rafae2k/Ultracif/Bibliografia/Arquivos PDF/N95 Filtering Facepiece Respirator Ultraviolet Germicidal Irradiation (UVGI) Process for Decontamination and Reuse.pdf

# N95 Filtering Facepiece Respirator Ultraviolet Germicidal Irradiation (UVGI) Process for Decontamination and Reuse

John J Lowe, Katie D Paladino, Jerald D Farke, Kathleen Boulter, Kelly Cawcutt, Mark Emodi, Shawn Gibbs, Richard Hankins, Lauren Hinkle, Terry Micheels, Shelly Schwedhelm, Angela Vasa, Michael Wadman, Suzanne Watson, and Mark E Rupp

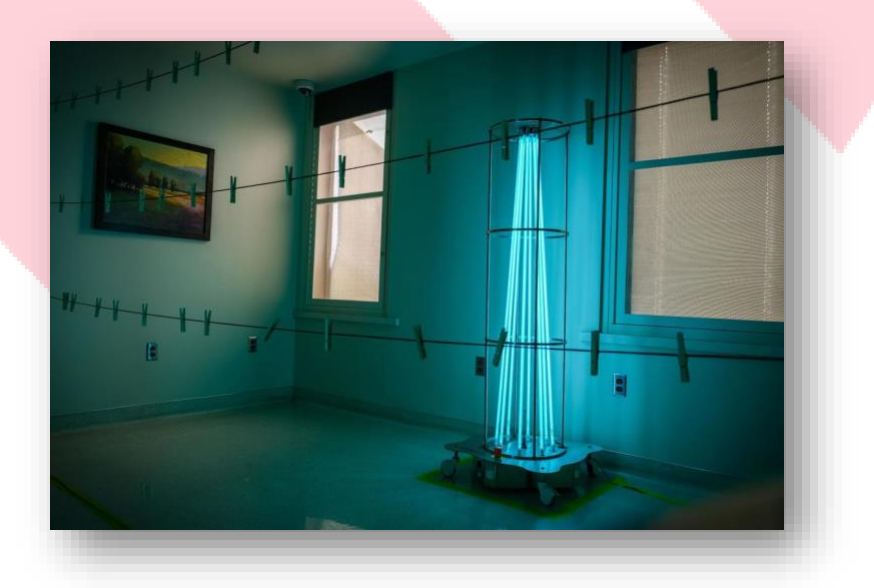
[picture p40: figure]

## Contents

## Table of Figures

Figure 1 – Room Setup (Overhead View). The lines holding the N95 FFRs are 13 feet long and hold 30 respirators per line (3 across the room); the UVGI “torches” are located 4 feet from the

Figure 6 – Log respirator drop-off (must note contact for pickup of respirators when

Figure 8 – Indicate name of respirator owner on new white bag, and number of respirators to

Figure 9 – Wipe cart thoroughly with Oxivir®
1 wipes. Doff at threshold and exit room. Perform

Figure 13 – While cycle runs, write name on new brown bag and place in corresponding labeled

Figure 14 – Run cycle until dose is not less than 300 mJ/cm²

Figure 21 – Contact staff indicated on drop-off log to communicate respirators are ready for

## Introduction

### Rationale and Method:

The ongoing pandemic of SARS-CoV-2 resulting in COVID-19 has severely stressed the worldwide healthcare system and has created dangerous shortages of personal protective equipment (PPE) including N95 filtering facepiece respirators (N95 FFRs). In an effort to extend the stockpile of N95 FFRs at our institution and reduce risks associated with reuse of untreated, contaminated N95 FFRs, we developed a surface decontamination procedure involving the delivery of ultraviolet germicidal irradiation (UVGI) to used N95 FFRs. The evidence base supporting this program includes: 1) UVGI has been shown to effectively inactivate a wide range of human pathogens including coronaviruses and other human respiratory viruses; 2) UVGI has been demonstrated to inactivate human respiratory viruses, including coronaviruses, on various models of N95 FFRs; 3) levels of UVGI needed to inactive human respiratory viruses are well below the level of irradiation that adversely affects the fit and filtration characteristics of N95 FFRs; and 4) UVGI can be safely administered when appropriate safeguards are in place. We also recognize there is uncertainty regarding how long an N95 FFR maintains properties to achieve adequate fit, requiring providers to inspect FFRs before and after reuse. Any organization considering a decontamination strategy (including UVGI, vaporized hydrogen peroxide, warm moist heat, etc.) to deal with lack of supply or potential lack of N95 FFR should validate their own procedures, including desired surrogate microbial reduction and retained filter efficiency and fit. Herein, we briefly describe our procedure to surface decontaminate and reuse N95 FFRs.

Literature supports UVGI exposures of 1 J/cm²
are capable of decontaminating influenza virus on N95 FFRs and exposures as low as of 2-5 mJ/cm²
are capable inactivating coronaviruses on surfaces (1-2). Given this range, we validated FFR UVGI exposures of 60 mJ/cm²
and 300
mJ/cm²
, from room sensors not from the surface of each mask, to reduce 6 log of bacterial and viral surrogate organisms. In our decontamination process, used N95 FFRs are subjected to UVGI at a room exposure of 300 mJ/cm²
. This exposure is measured for one of the two UVGI sources and from a location that receives the lowest UVGI dose---this does not represent the dose on the surface of each N95 FFR. Exposure mapping of our system indicated N95 FFR received a dose of double the measured dose from each side of the N95 FFR. Single-stranded RNA viruses, such as SARS-CoV-2, are generally inactivated by UVGI exposure of 2-5 mJ/cm² (2). Thus, the UVGI exposure we have chosen exceeds, by at least several fold, the amount of exposure needed to inactivate SARS-CoV-2 and provides a wide margin of safety for surface decontamination.

Respirators are secured on wires that are strung across a room with two UVGI towers (ClorDiSys UVGI Light System, https://www.clordisys.com/products.php) on either side. Each of the two UVGI towers are equipped with eight 254 nm bulbs, these bulbs are routinely used in biosafety cabinets and produce 200 μw/cm²
at 10 feet distance for a dosage of 12 mJ/minute. We monitor the delivered UVGI exposure dose with a room UVGI meter that can be initiated and monitored from outside the room to verify that the desired exposure has been achieved. As UVGI can cause damage to eyes and skin, this protects our UVGI associate’s safety. We plan to decontaminate and reuse the N95 FFRs multiple times until respirator fit is impacted (3-5). Prior to initiating the decontamination program, the walls and ceiling were covered with a UV-reflective coating (https://lumacept.com) with which our group had experience (5). Our program initially involved the units with high N95 FFR use such as the emergency department and our COVID-19 ward, but we plan to rapidly expand to ambulatory settings. We believe a variety of UV light sources could be used in a similar fashion including UV equipped biosafety or sterilization cabinets or other UV disinfection systems and that this method can be applied to a variety of other critical items such as procedure masks. The method described below is a result of multiple tests, a review of the scientific literature, and incorporation of current institutional practice.

## UVGI Room Setup

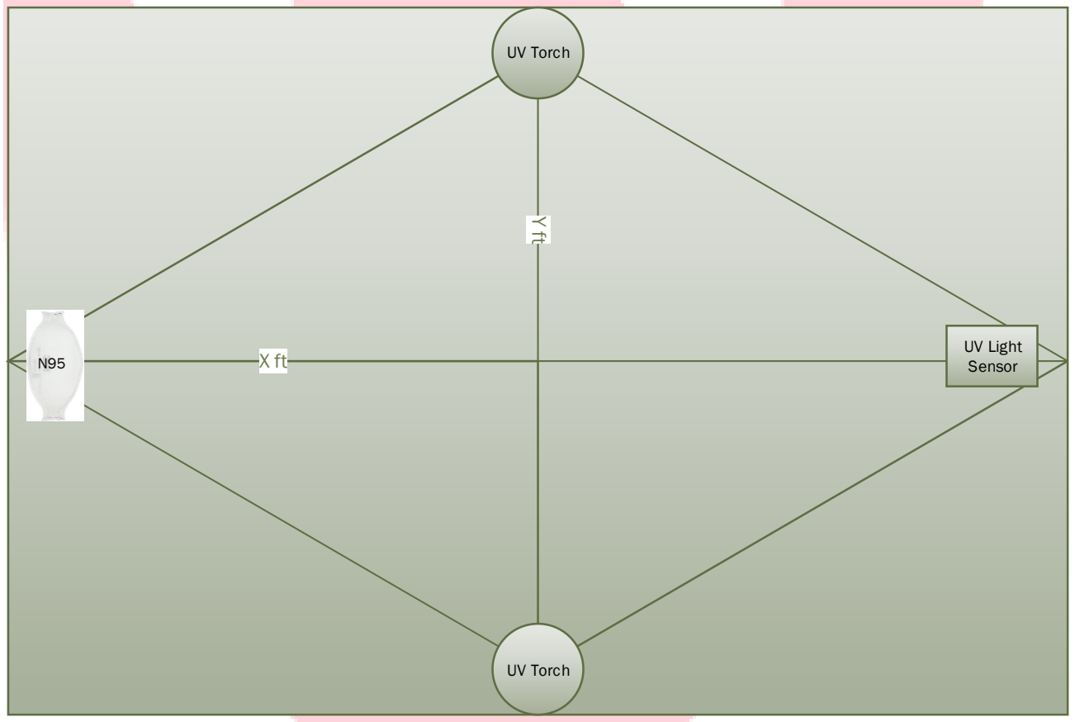
[picture p41: figure]
UV Torch; UV Torch Y ft; UV Light; Sensor

Figure 1 – Room Setup (Overhead View). The lines holding the N95 FFRs are 13 feet long and hold 30 respirators per line (3 across the room); the UVGI “torches” are located 4 feet from the center of the line and are 8 feet apart.

## Process Map

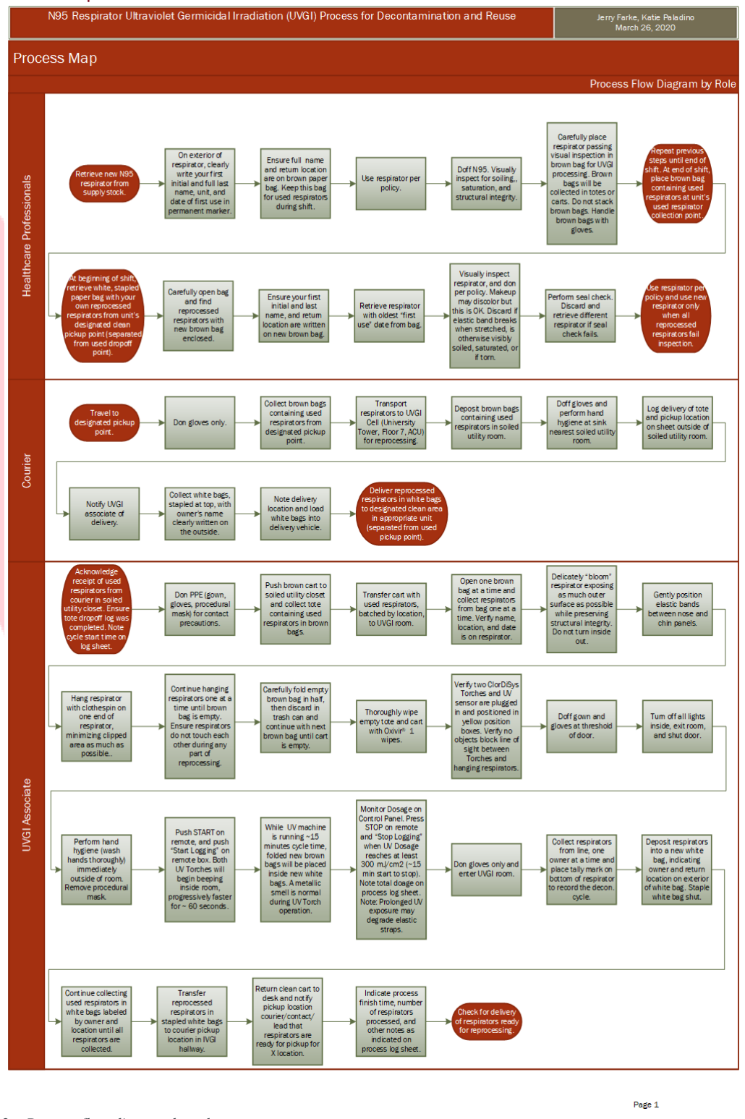
[picture p42: figure]

Figure 2 – Process flow diagram by role

## Roles

### Healthcare Professional (HCP)

- Healthcare Professional retrieves new N95 FFR from secure Omnicell storage or other storage location
- Using a permanent marker, HCP writes needed information on front of respirator including first initial and last name, department/unit location*, and date of first use*. (This ensures correct respirator is returned to correct HCP and to the correct location; Date of first use is requested to monitor duration of use as well as number of decontamination cycles)
- HCP dons N95 FFR per policy ensuring integrity of respirator and proper fit
- HCP uses N95 FFR following extended use guidelines per policy (https://www.nebraskamed.com/sites/default/files/documents/covid-19/COVID-Extended-Use-Reuse-of-PPE-and-N95.pdf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) (https://www.nebraskamed.com/sites/default/files/documents/covid-19/COVID-Extended-Use-Reuse-of-PPE-and-N95.pdf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)
Upon doffing:
- Remove N95 FFR following appropriate doffing guidelines
- Place used N95 FFR in brown paper bag ensuring brown bag is correctly labeled with HCP full name, and Department/Unit return location
- When ready to send brown bag, with used respirators, for decontamination, the HCP brings bag to department/unit designated “dirty” drop off location. This is separate from the department/unit “clean” location.
Specific to In-House Staff
- Donning gloves only, staff courier collects all used respirators (in brown bags) in a cart or tote.
- Staff courier takes cart/tote to Decontamination Unit. Only gloves need to be worn for this process.
- Staff courier places department/unit supply of brown bags (containing used respirators) in the Decontamination Unit’s Dirty Storage area. Staff courier places tote or individual bags on the shelf designated for specific unit.
- Staff courier removes gloves and performs hand hygiene
- Staff courier logs requested information onto the drop off log sheet (name of individual dropping off, contact number, department/unit location, name of person to contact for pick up, pick up contact number)
Specific to Ambulatory Clinic and Immediate Care Clinic Staff
- Lidded tote, with brown bags containing used respirators, is picked up by courier from clinic site’s designated location. Pick-ups are done at times specific to clinic site. Any used respirators, needing decontaminated, must be placed in tote prior to the specified pick up time.

Upon Completion of Decontamination Process:
Specific to In-House Staff
- The Decontamination unit calls contact person, provided on log sheet, to notify that department/unit decontaminated respirators are ready for pick up.
- Staff courier dons gloves and retrieves decontaminated respirators from the Decontamination Unit’s designated clean pick up area.

- Decontaminated respirators are in new, clean white bags displaying HCP’s and return location. A new brown bag is included in the clean white bag to serve as new “dirty” discard brown bag.
- Staff courier logs name and time of pick up on the log sheet
- White bags are returned to department/unit designated clean pick up location.
- HCP will notice a tally mark has been added, by the UVGI associate, after decontamination process, to track the number of times a particular mask has gone through the decontamination.

Specific to Ambulatory Clinic and Immediate Care Clinic Staff
- Clean white bags (containing decontaminated respirators) are returned, by courier, to each site’s designated “clean” delivery location. White bags are labeled (by decontamination personnel) with each HCP’s name and site location. A new brown bag is included in the clean white bag to serve as new “dirty” discard brown bag.
- HCP will notice a tally mark has been added, by the UVGI associate, after decontamination process, to track the number of times a particular mask has gone through the decontamination.
- Deliveries to clinic or ICC site are conducted at a time specific to site location.

* A note specific to in-house float staff: For HCP floating between multiple units, HCP may designate their unit/department as the most recently worked resulting in their white bag, with decontaminated bags, being returned to that location or, HCP may write “Float” as their unit/department location. For HCP that designate their location as “Float”, their white bag, with decontaminated respirators, need be picked up personally in the Decontamination Unit’s clean storage location designated for float staff.

### UVGI Associate

- Acknowledge receipt of used respirators from courier in soiled utility closet. Ensure tote drop-off log was completed. Note cycle start time on log sheet.
- Don PPE (gown, gloves, procedural mask) for contact precautions.
- Push brown cart to soiled utility closet and collect tote containing used respirators in brown bags.
- Transfer cart with used respirators, batched by location, to UVGI room.
- Open one brown bag at a time and collect respirators from bag one at a time. Verify name, location, and date is on respirator.
- Delicately “bloom” respirator exposing as much outer surface as possible while preserving structural integrity. Do not turn inside out.
- Gently position elastic bands between nose and chin panels, if applicable.
- Hang respirator with clothespin on one end of respirator, minimizing the clipping area as much as possible.
- Continue hanging respirators one at a time until brown bag is empty. Ensure respirators do not touch each other during any part of reprocessing.
- Carefully fold empty brown bag in half, then discard in trash can and continue with next brown bag until cart is empty.

- Thoroughly wipe empty tote and cart with Oxivir® 1 wipes.
- Verify two ClorDiSys Torches and UVGI sensor are plugged in and positioned in yellow position boxes. Verify no objects block line of sight between Torches and hanging respirators.
- Doff gown and gloves at threshold of door.
- Turn off all lights inside, exit room, and shut door.
- Perform hand hygiene (wash hands thoroughly) immediately outside of room. Remove procedural mask.
- Push START on remote, and push “Start Logging” on UVGI meter box. Both UVGI Torches will begin beeping inside room, progressively faster for ~ 60 seconds.
- While UVGI machine is running ~5 minutes cycle time, folded new brown bags will be placed inside new white bags. A metallic smell is normal during UV Torch operation.
- Monitor Dosage on Control Panel. Press STOP on remote and “Stop Logging” when UV Dosage reaches at least 300 mJ/cm² (~5-6 min start to stop). Note elapsed time and total dosage on process log sheet. Note: Prolonged UVGI exposure may degrade elastic straps.
- Don gloves only and enter UVGI room.
- Collect respirators from line, one owner at a time and place tally mark on bottom of respirator to record the decontamination cycle.
- Deposit respirators into a new white bag, indicating owner and return location on exterior of white bag. Staple white bag shut.
- Continue collecting used respirators in white bags labeled by owner and location until all respirators are collected.
- Transfer reprocessed respirators in stapled white bags to courier clean pickup location in UVGI hallway.
- Return clean cart to desk and notify pickup location courier/contact/lead that respirators are ready for pickup for their location.
- Indicate process finish time, number of respirators processed, and other notes as indicated on process log sheet.
- Check for delivery of respirators ready for reprocessing.

## Appendix

### Process Photos

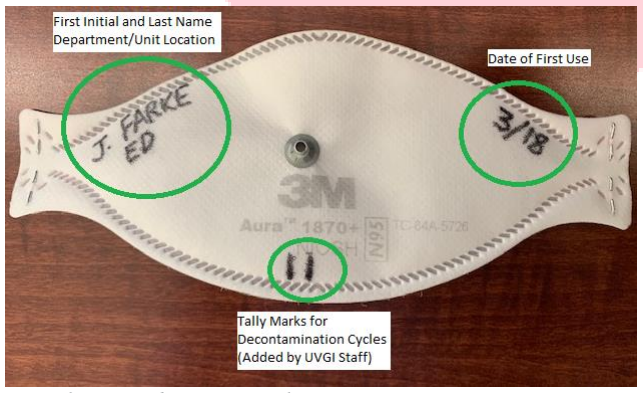
[picture p43: figure]

Figure 3 - Required respirator markings.

Courier

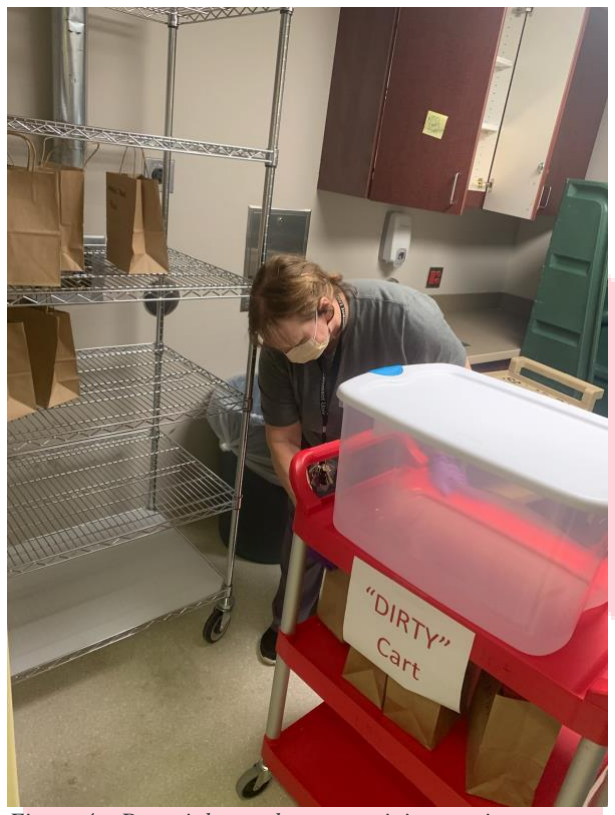
[picture p44: figure]

Figure 4 – Deposit brown bags containing respirators on rack in soiled utility room.

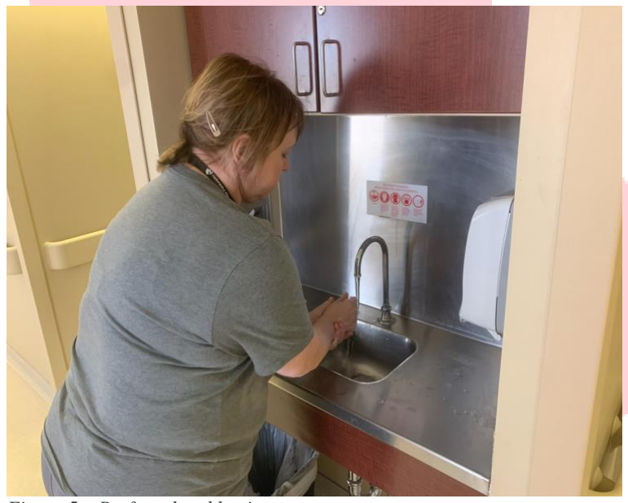
[picture p45: figure]

Figure 5 – Perform hand hygiene.

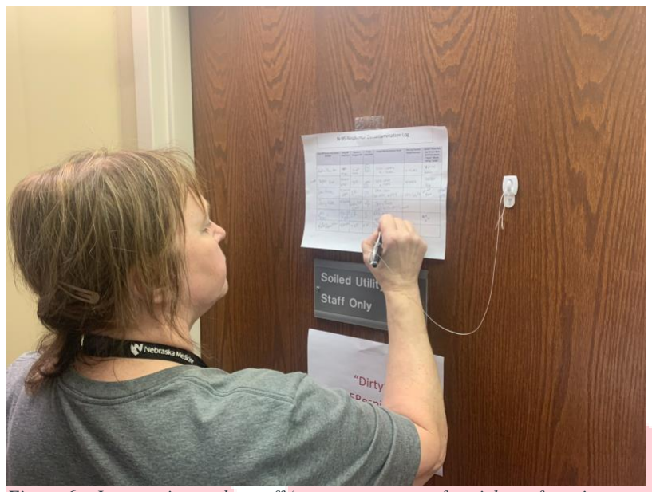
[picture p46: figure]

Figure 6 – Log respirator drop-off (must note contact for pickup of respirators when decontaminated).
UVGI Associate

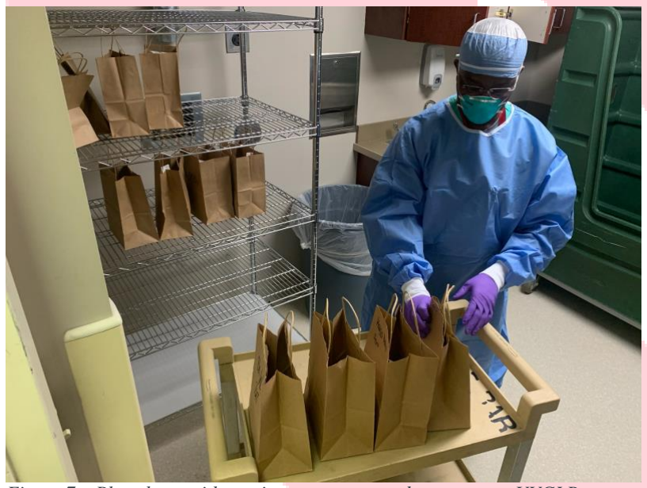
[picture p47: figure]

Figure 7 – Place bags with respirators on cart and transport to UVGI Room.

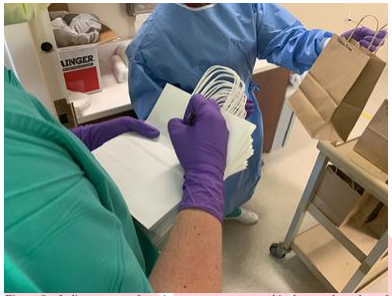
[picture p48: figure]

Figure 8 – Indicate name of respirator owner on new white bag, and number of respirators to return.

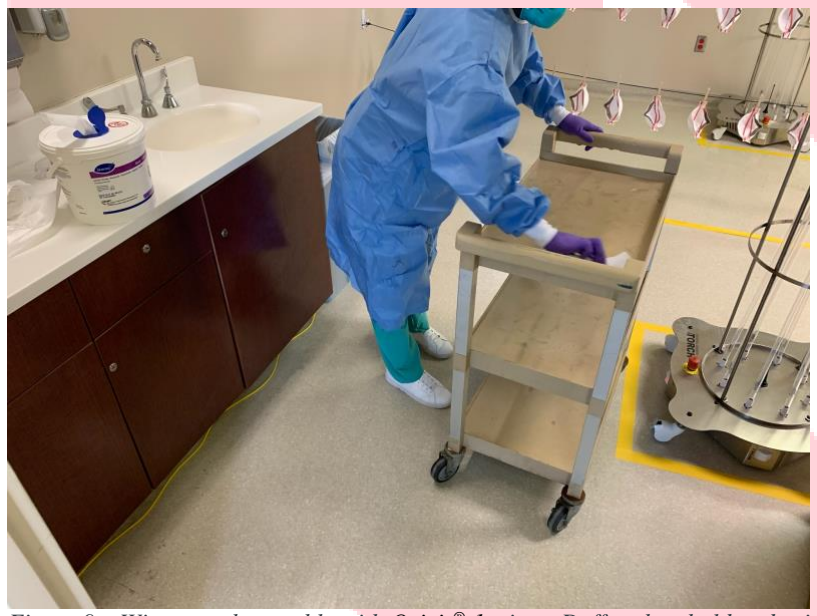
[picture p49: figure]

Figure 9 – Wipe cart thoroughly with Oxivir® 1 wipes. Doff at threshold and exit room. Perform hand hygiene.

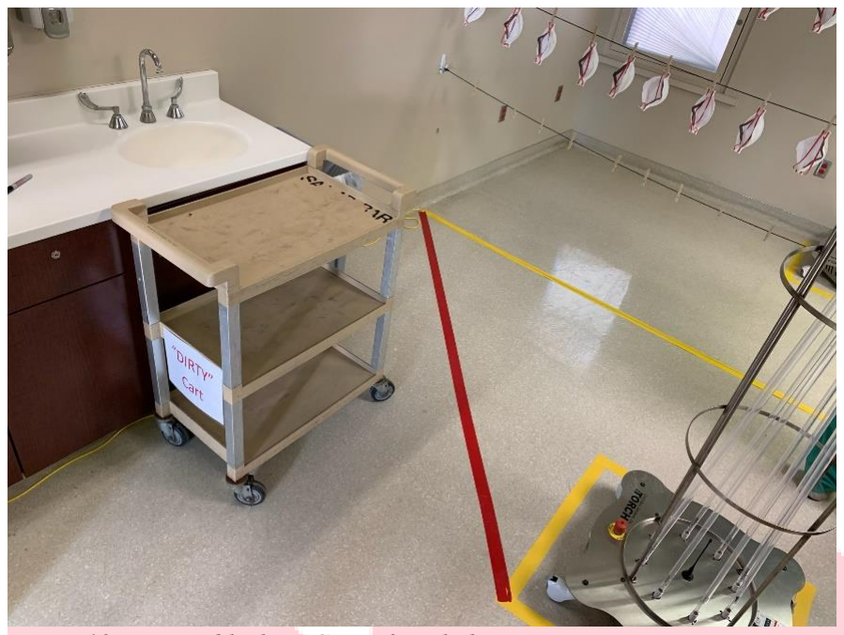
[picture p50: figure]

Figure 10 – Do not block UVGI arc from light to respirators.

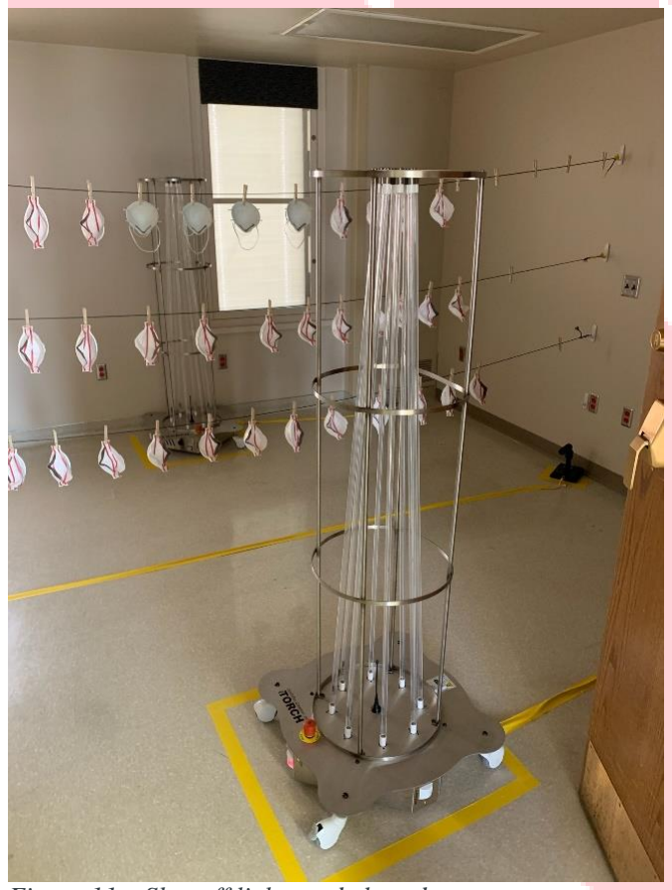
[picture p51: figure]

Figure 11 – Shut off lights and close door.

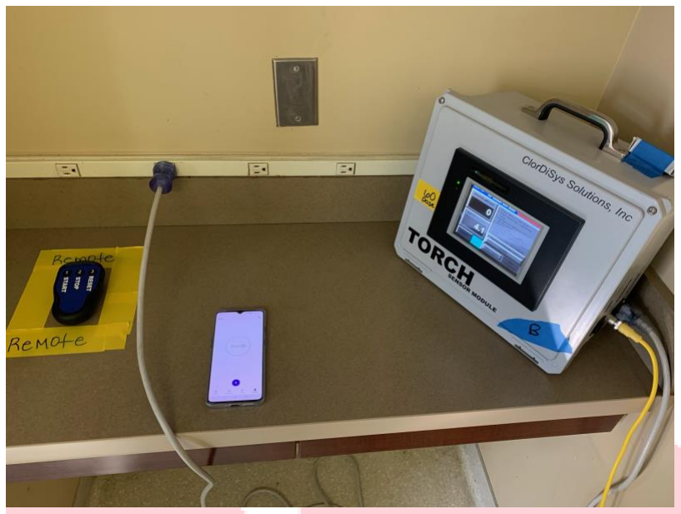
[picture p52: figure]

Figure 12 – Start cycle on remote. Start logging on touchscreen.

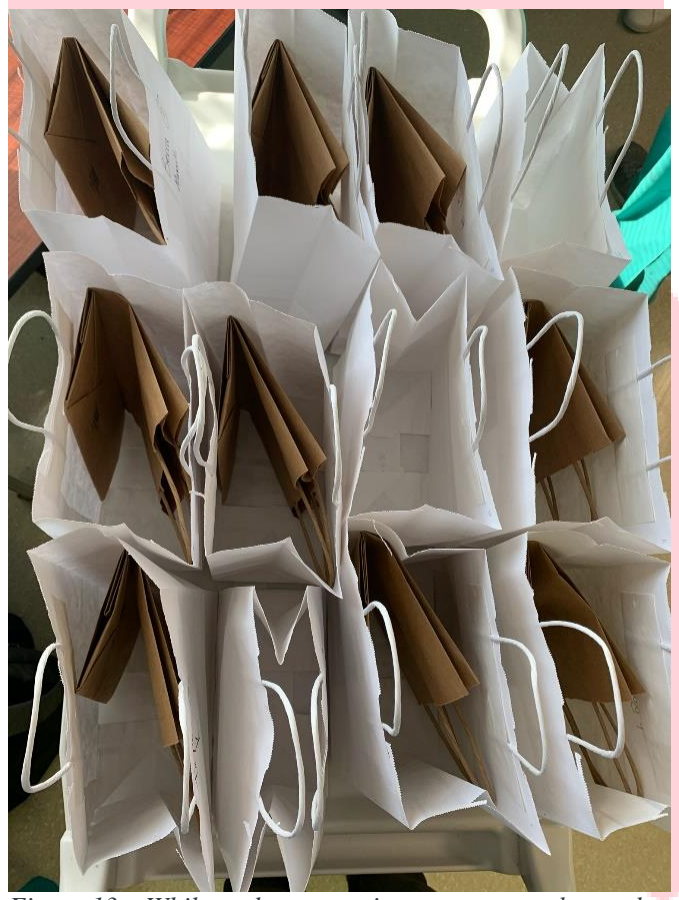
[picture p53: figure]

Figure 13 – While cycle runs, write name on new brown bag and place in corresponding labeled white bag.

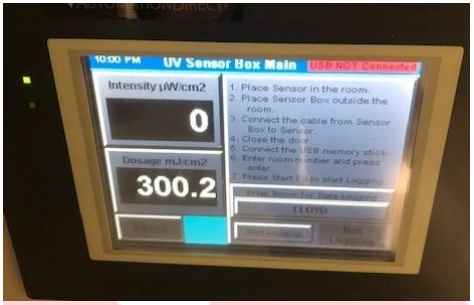
[picture p54: figure]

Figure 14 – Run cycle until dose is not less than 300 mJ/cm² .

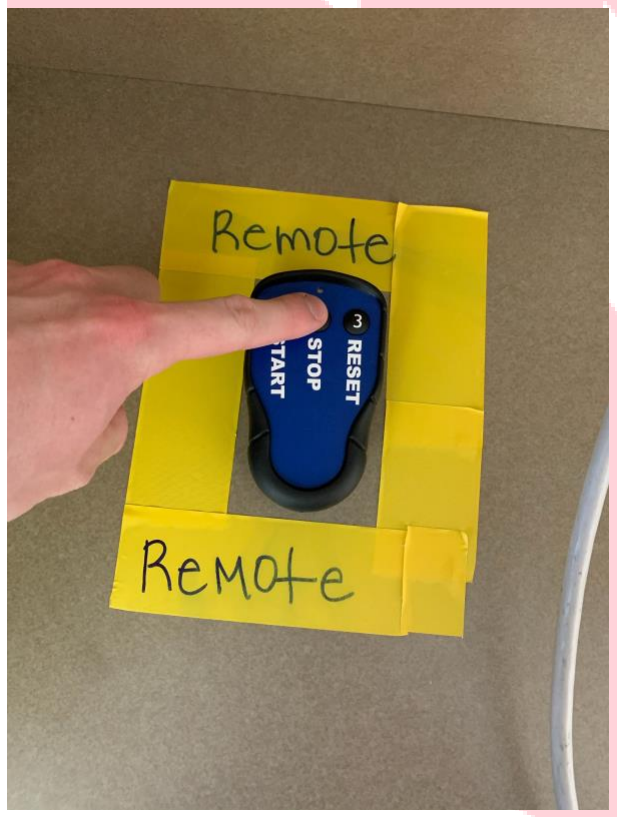
[picture p55: figure]

Figure 15 – Stop cycle on remote as soon as possible after minimum required dose.

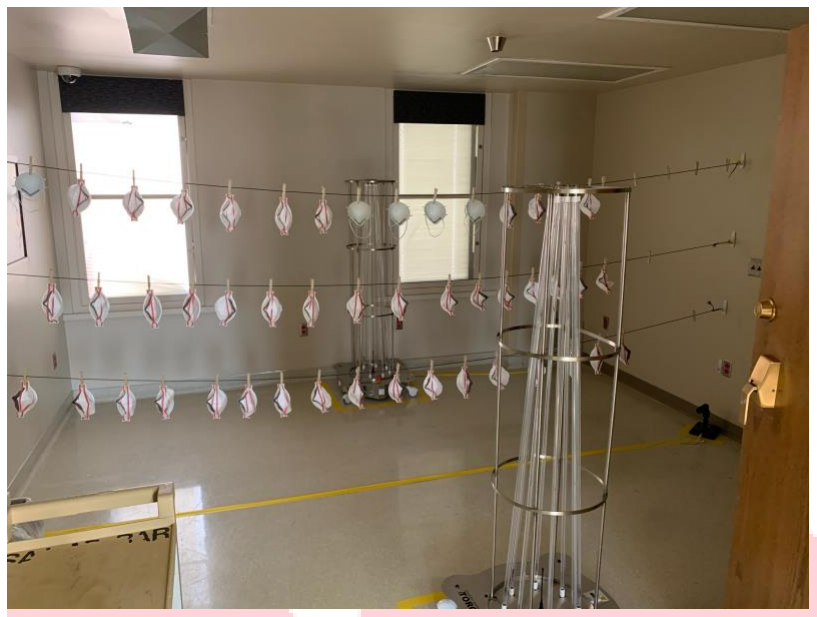
[picture p56: figure]

Figure 16 – Enter room with gloves and procedure mask.

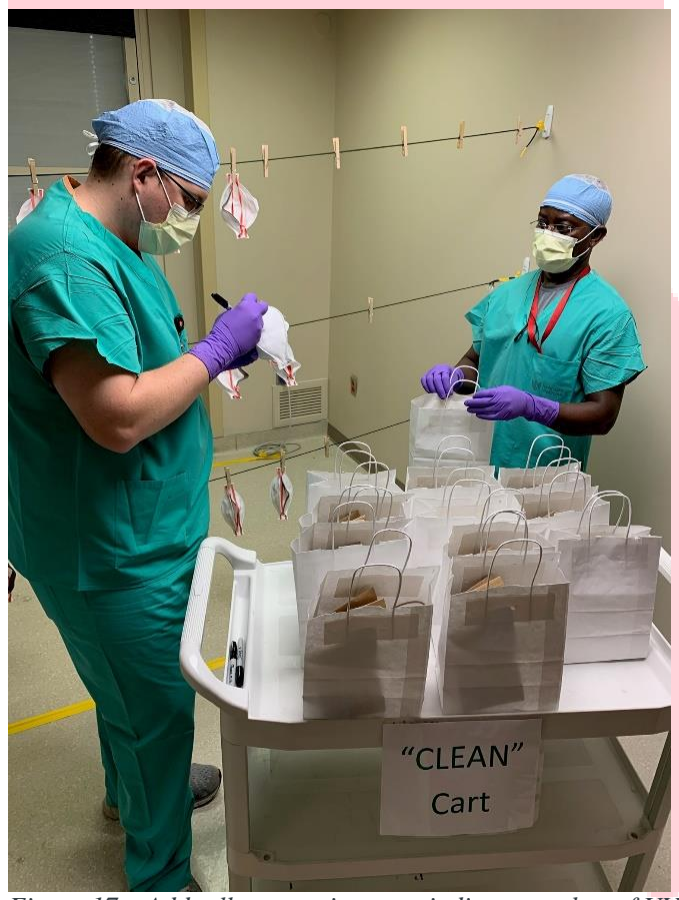
[picture p57: figure]

Figure 17 – Add tally to respirator to indicate number of UVGI cycles.

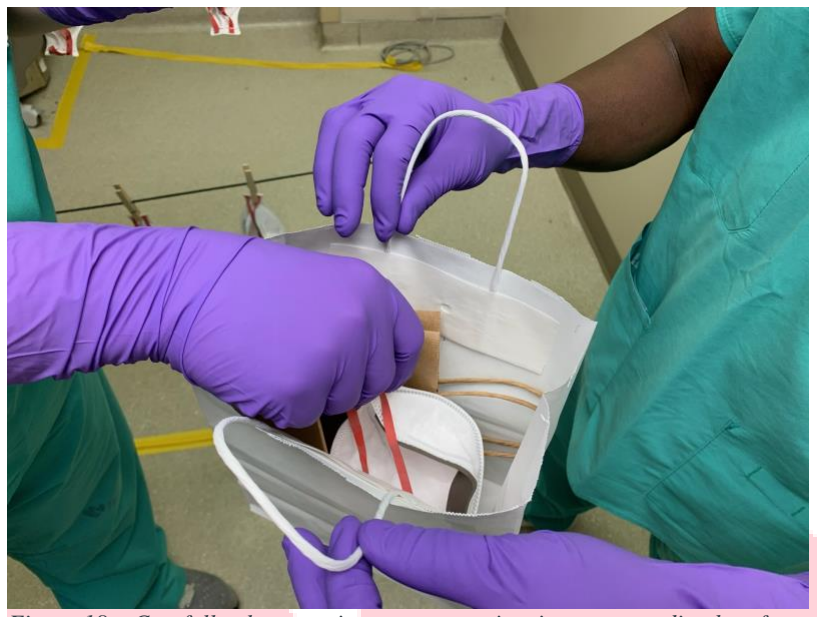
[picture p58: figure]

Figure 18 – Carefully place respirator one at a time in corresponding bag for each owner.

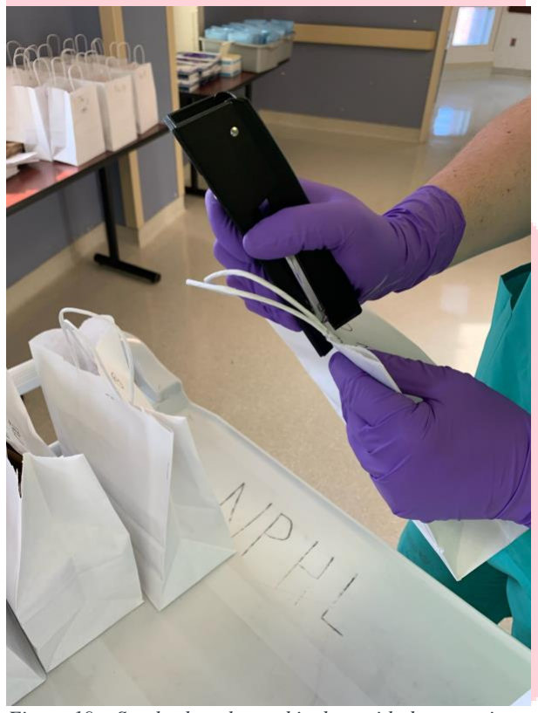
[picture p59: figure]

Figure 19 – Staple shut clean white bag with decontaminated respirators.

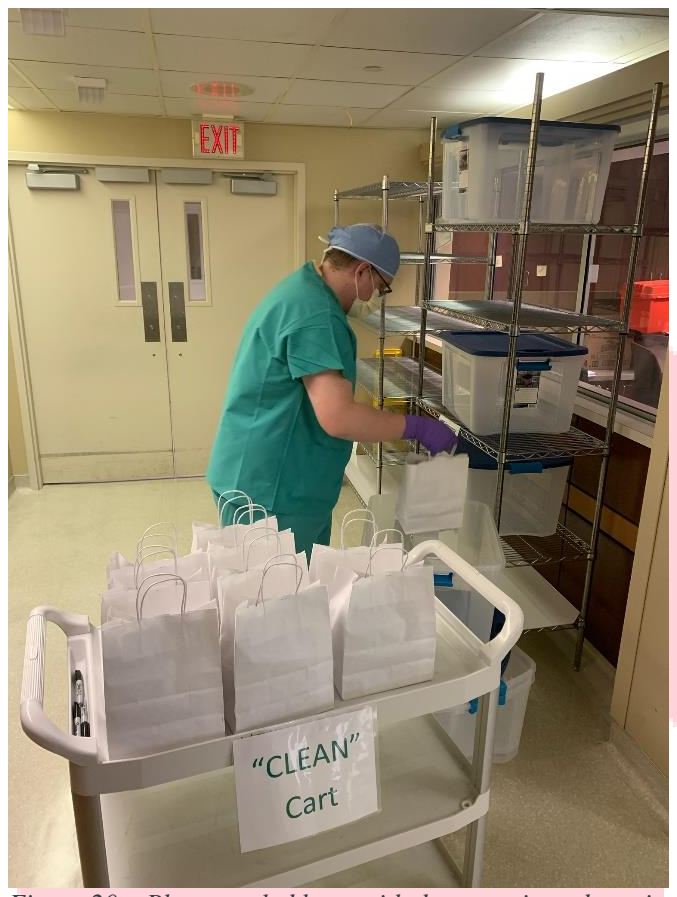
[picture p60: figure]

Figure 20 – Place stapled bags with decontaminated respirators in totes.

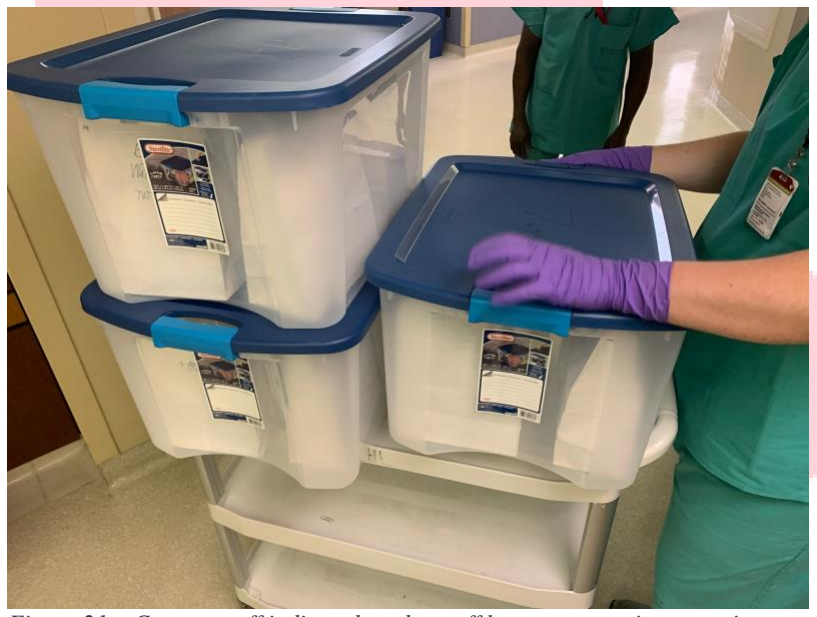
[picture p61: figure]

Figure 21 – Contact staff indicated on drop-off log to communicate respirators are ready for pickup.

References:
1. Mills, Devin, Delbert A. Harnish, Caryn Lawrence, Megan Sandoval-Powers, and Brian
K. Heimbuch. "Ultraviolet germicidal irradiation of influenza-contaminated N95 filtering facepiece respirators." American journal of infection control46, no. 7 (2018): e49-e55. https://doi.org/10.1016/j.ajic.2018.02.018
2. Chun-Chieh Tseng & Chih-Shan Li (2007) Inactivation of Viruses on Surfaces by Ultraviolet Germicidal Irradiation, Journal of Occupational and Environmental Hygiene, 4:6, 400-405, DOI: 10.1080/15459620701329012 (https://doi.org/10.1080/15459620701329012)
3. Michael B. Lore, Brian K. Heimbuch, Teanne L. Brown, Joseph D. Wander, Steven H. Hinrichs, Effectiveness of Three Decontamination Treatments against Influenza Virus Applied to Filtering Facepiece Respirators, The Annals of Occupational Hygiene,
Volume 56, Issue 1, January 2012, Pages 92–101. https://doi.org/10.1093/annhyg/mer054
4. Dennis J. Viscusi, Michael S. Bergman, Benjamin C. Eimer, Ronald E. Shaffer, Evaluation of Five Decontamination Methods for Filtering Facepiece Respirators, The Annals of Occupational Hygiene, Volume 53, Issue 8, November 2009, Pages 815–
827. https://doi.org/10.1093/annhyg/mep070
5. William G. Lindsley, Stephen B. Martin Jr., Robert E. Thewlis, Khachatur Sarkisian, Julian O. Nwoko, Kenneth R. Mead & John D. Noti (2015) Effects of Ultraviolet Germicidal Irradiation (UVGI) on N95 Respirator Filtration Performance and Structural Integrity, Journal of Occupational and Environmental Hygiene, 12:8, 509-
517. DOI: 10.1080/15459624.2015.1018518 (https://doi.org/10.1080/15459624.2015.1018518)
6. Katelyn C. Jelden, Shawn G. Gibbs, Philip W. Smith, Angela L. Hewlett, Peter C. Iwen, Kendra K. Schmid & John J. Lowe (2017) Ultraviolet (UV)-reflective paint with ultraviolet germicidal irradiation (UVGI) improves decontamination of nosocomial bacteria on hospital room surfaces, Journal of Occupational and Environmental Hygiene, 14:6, 456-460. DOI: 10.1080/15459624.2017.1296231 (https://doi.org/10.1080/15459624.2017.1296231)
