rafae2k/Ultracif/CAD/Impressao 3D/3MF/Bucha Rolamento + Suporte Rolamento + Suporte Aro - IMPRIMIR 1 LOTE.3mf

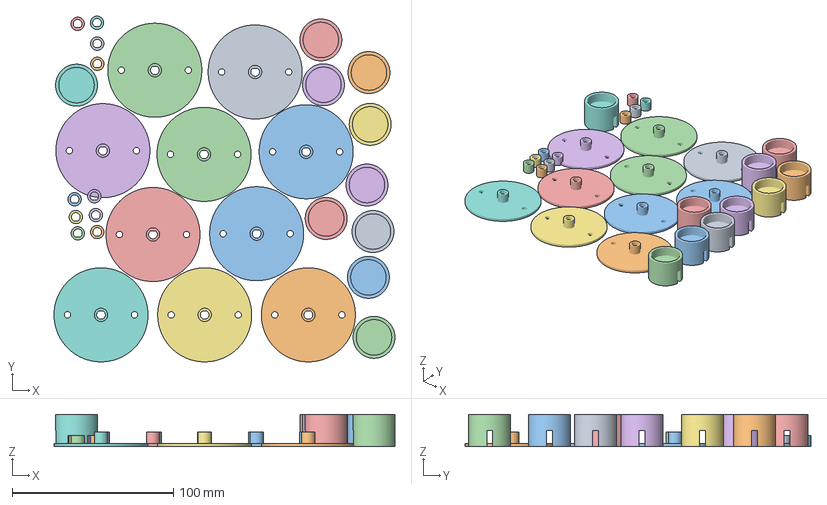
[picture p78: CAD file, 2020-10-14]
CAD/Impressao 3D/3MF/Bucha Rolamento + Suporte Rolamento + Suporte Aro - IMPRIMIR 1 LOTE.3mf
211.4 x 214.4 x 20.0 mm
bucha rolamento.stl
bucho.stl
Suporte Rolamento.stl
