rafae2k/Ultracif/CAD/Plano de Corte/Peças Individuais/Externo/LAMP 400 - Aleta 4.dxf

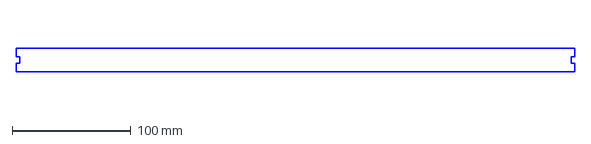
[picture p79: CAD file, 2020-10-14]
CAD/Plano de Corte/Peças Individuais/Externo/LAMP 400 - Aleta 4.dxf
471.2 x 20.2 mm
