rafae2k/Ultracif/CAD/Plano de Corte/Peças Individuais/Externo/LAMP 400 - Lateral Esquerda.dxf

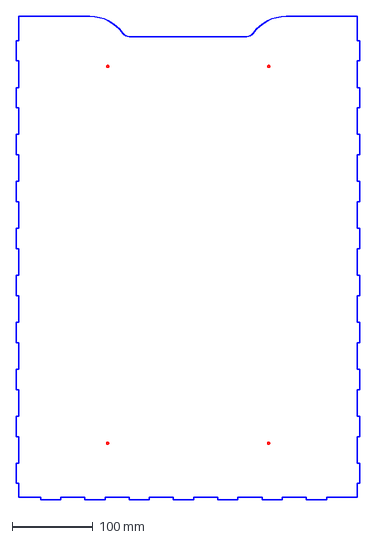
[picture p80: CAD file, 2020-10-14]
CAD/Plano de Corte/Peças Individuais/Externo/LAMP 400 - Lateral Esquerda.dxf
426.1 x 600.2 mm
