rafae2k/Ultracif/CAD/Plano de Corte/Peças Individuais/Externo/LAMP 400 - Aro 2.dxf

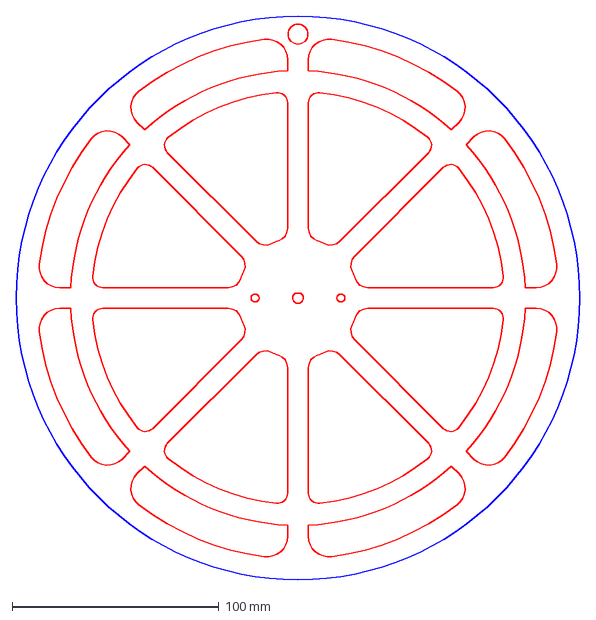
[picture p81: CAD file, 2020-10-14]
CAD/Plano de Corte/Peças Individuais/Externo/LAMP 400 - Aro 2.dxf
272.8 x 272.8 mm
