rafae2k/Ultracif/CAD/Plano de Corte/Peças Individuais/Externo/LAMP 400 - Barreira.dxf

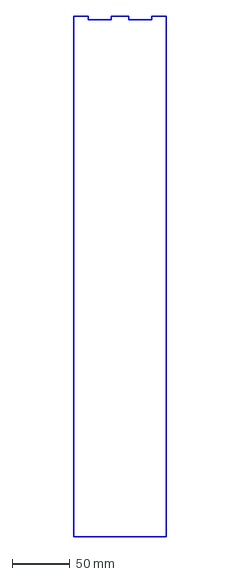
[picture p82: CAD file, 2020-10-14]
CAD/Plano de Corte/Peças Individuais/Externo/LAMP 400 - Barreira.dxf
80.3 x 450.1 mm
