rafae2k/Ultracif/CAD/Plano de Corte/Peças Individuais/Externo/LAMP 400 - Aleta 2.dxf

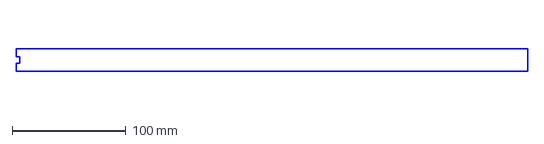
[picture p83: CAD file, 2020-10-14]
CAD/Plano de Corte/Peças Individuais/Externo/LAMP 400 - Aleta 2.dxf
450.2 x 20.2 mm
