rafae2k/Ultracif/Eletroeletronica/PCB/gerbers/UltraCif-B_Cu.pdf

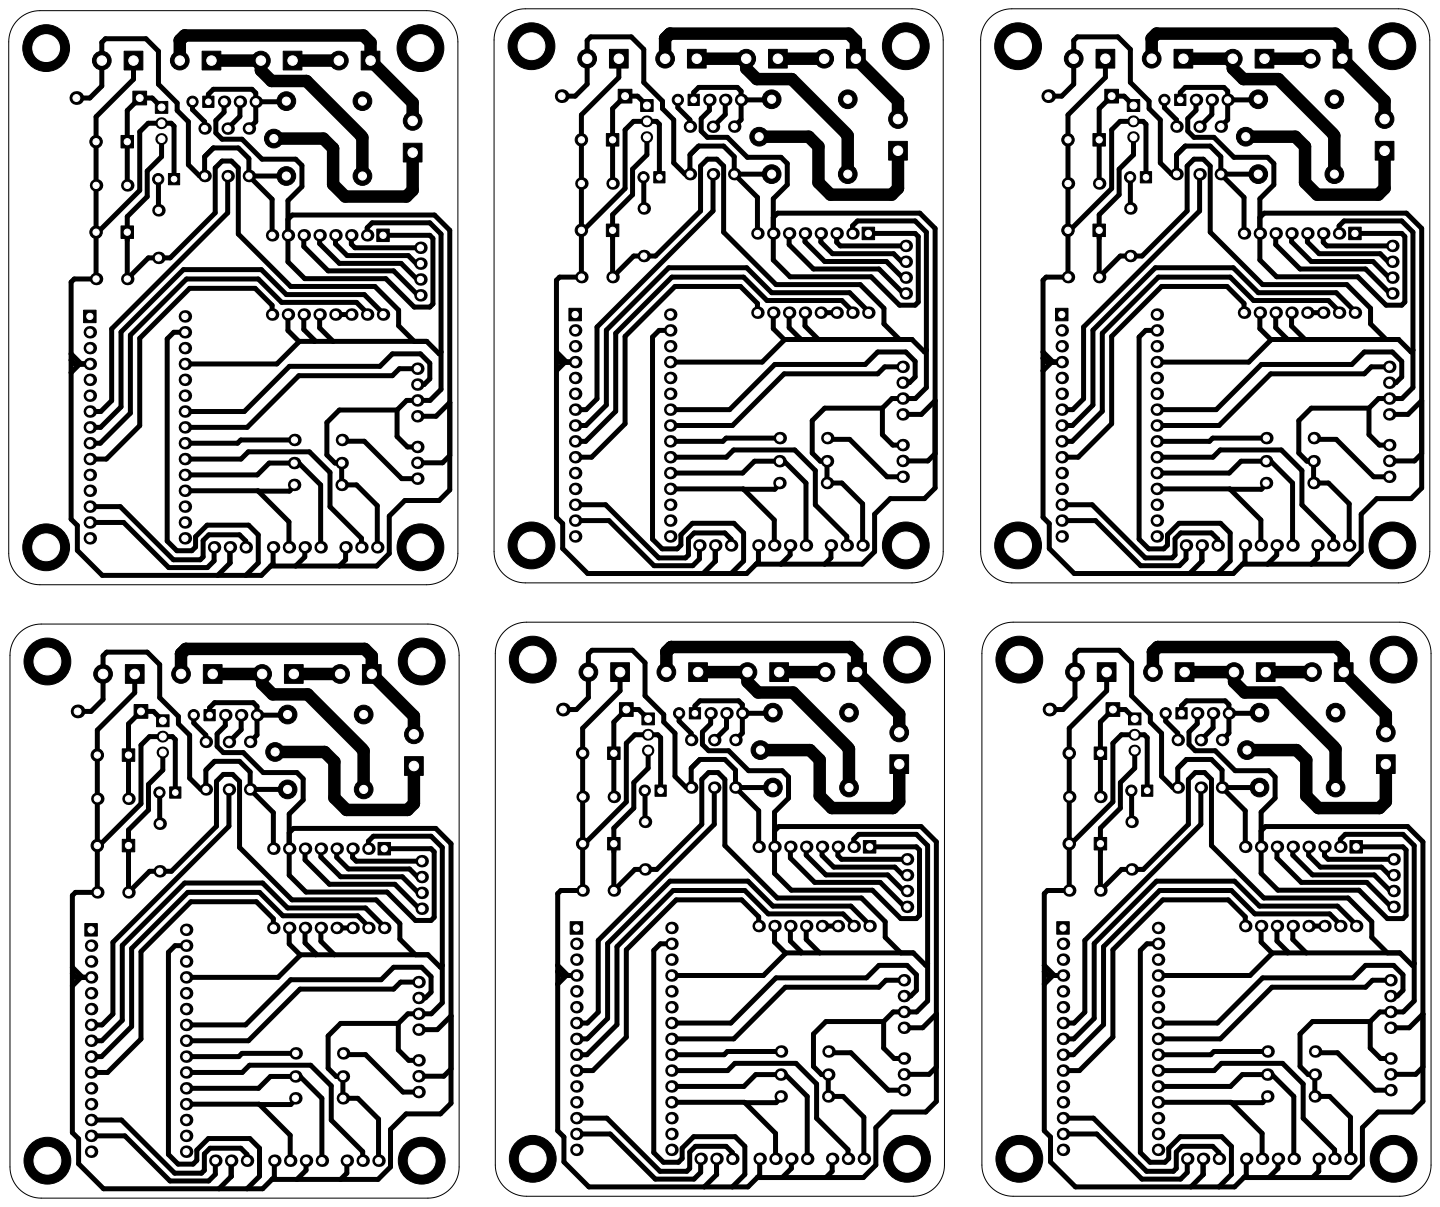
[picture p104: page 1]
